stasiselectronics/BatteryBoost/Images/Renders/2021.05.17/2021_05_17_3.png

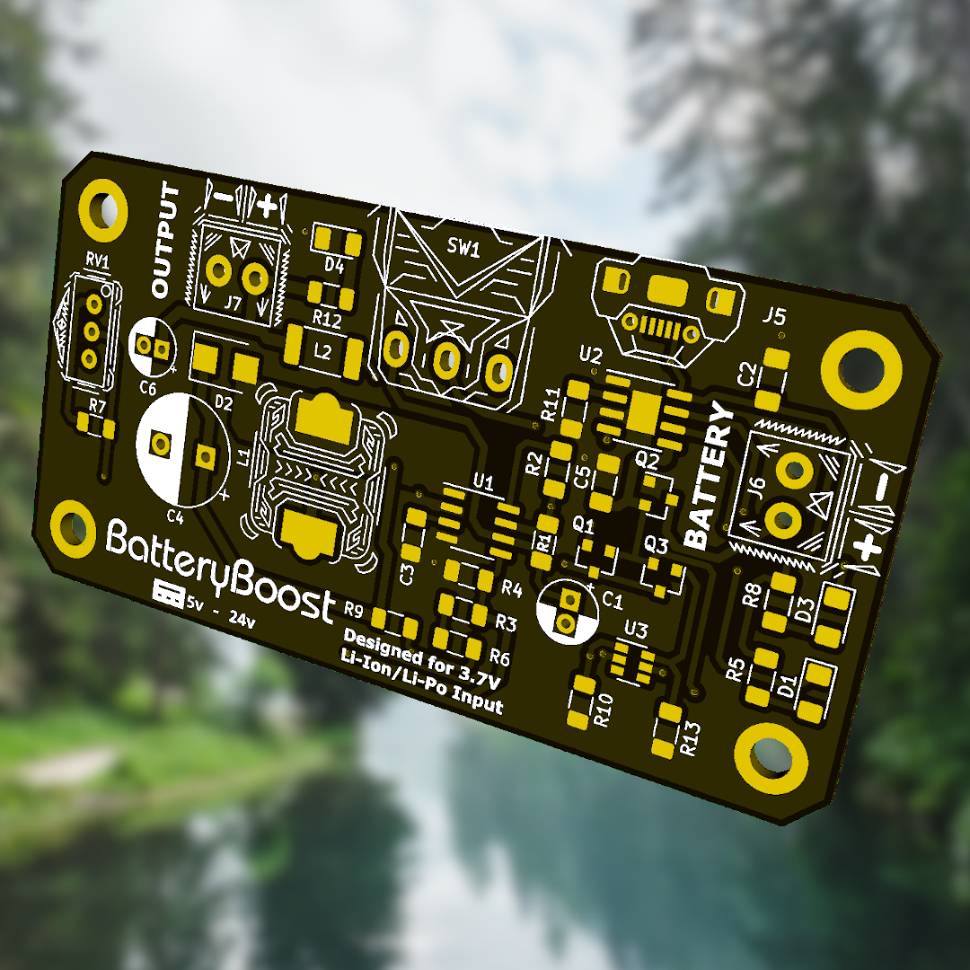
Images/Renders/2021.05.17/2021_05_17_3.png
